custom-ds/Universal-Remote-LIRC/GUI/assets/gra-background.png

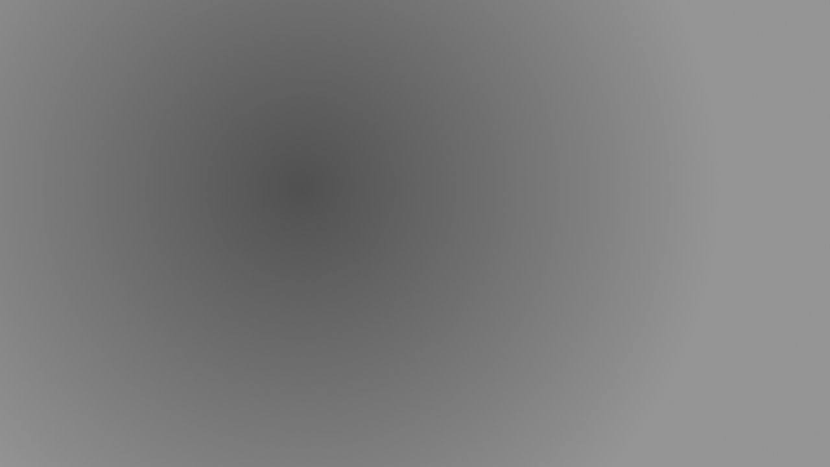
GUI/assets/gra-background.png
