custom-ds/Universal-Remote-LIRC/GUI/assets/whi-background.png

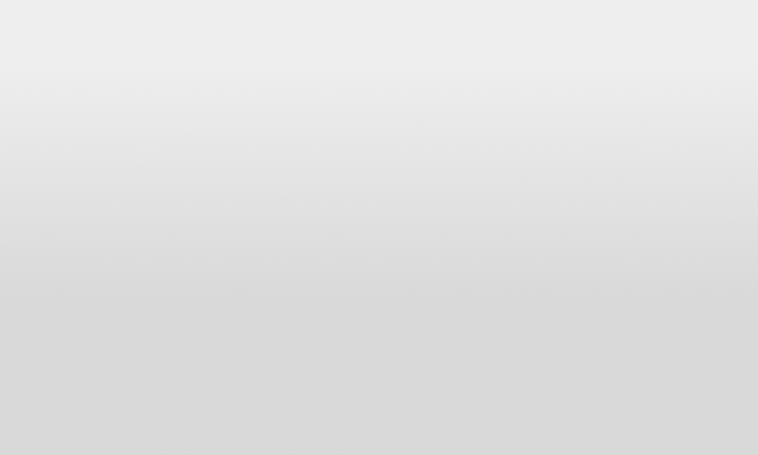
GUI/assets/whi-background.png
